saaimulation/Project-Aero/practice-lap-CAD/screenshots/3rdflap.png

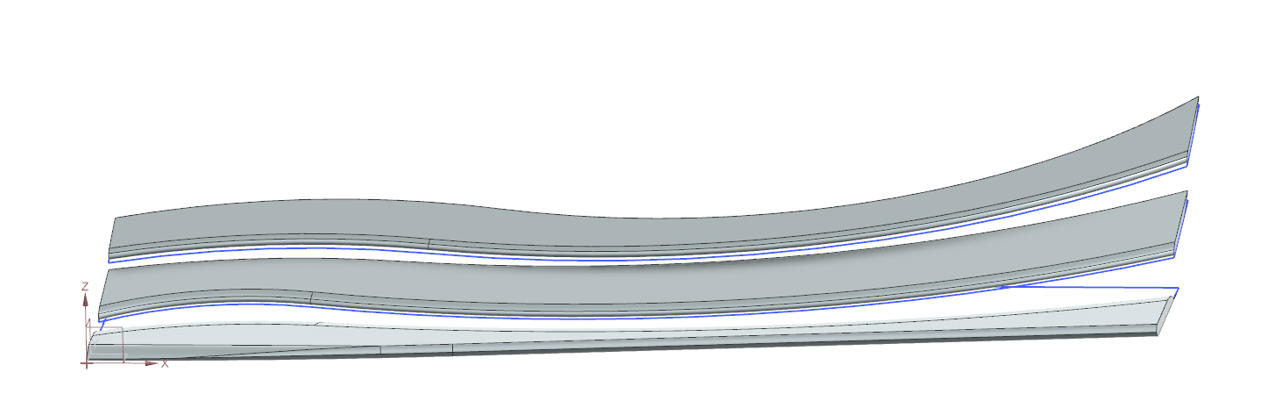
practice-lap-CAD/screenshots/3rdflap.png
