saaimulation/Project-Aero/practice-lap-CAD/screenshots/aerofoilshape.png

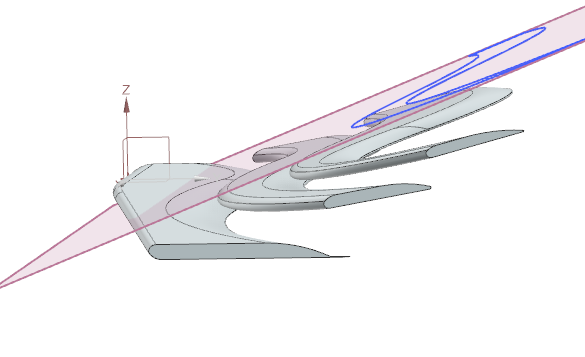
practice-lap-CAD/screenshots/aerofoilshape.png
