saaimulation/Project-Aero/practice-lap-CAD/screenshots/endplateedge.png

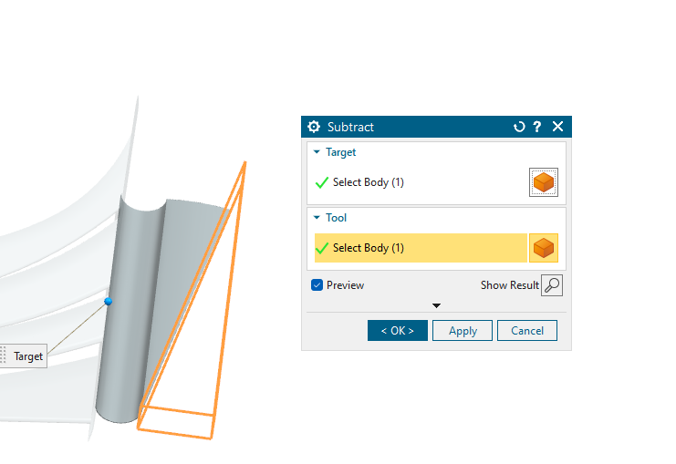
practice-lap-CAD/screenshots/endplateedge.png
