saaimulation/Project-Aero/practice-lap-CAD/screenshots/lines.png

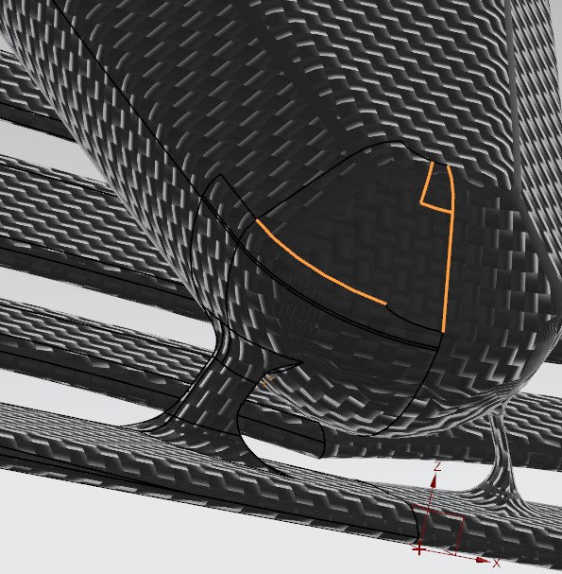
practice-lap-CAD/screenshots/lines.png
