saaimulation/Project-Aero/practice-lap-CAD/screenshots/sideview.png

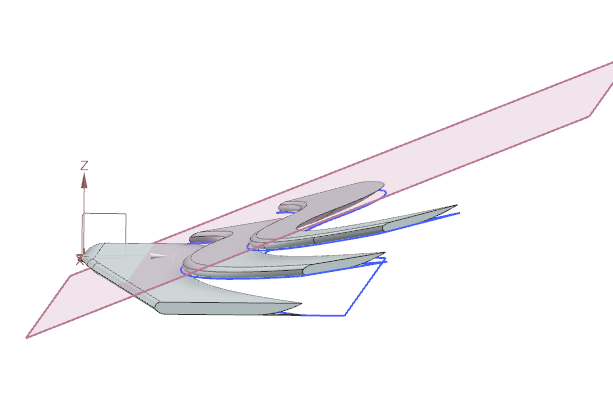
practice-lap-CAD/screenshots/sideview.png
