saaimulation/Project-Aero/qualifying-1-CFD/media/cfderror4.png

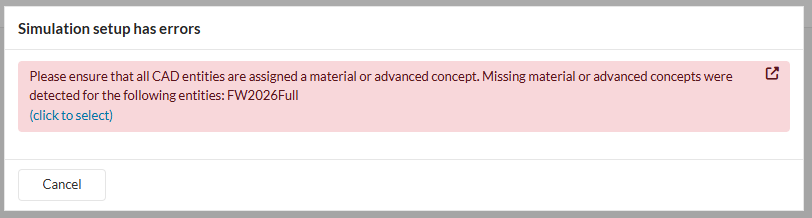
qualifying-1-CFD/media/cfderror4.png
