saaimulation/Project-Aero/sprint-3D-printing/images/finalprint.png

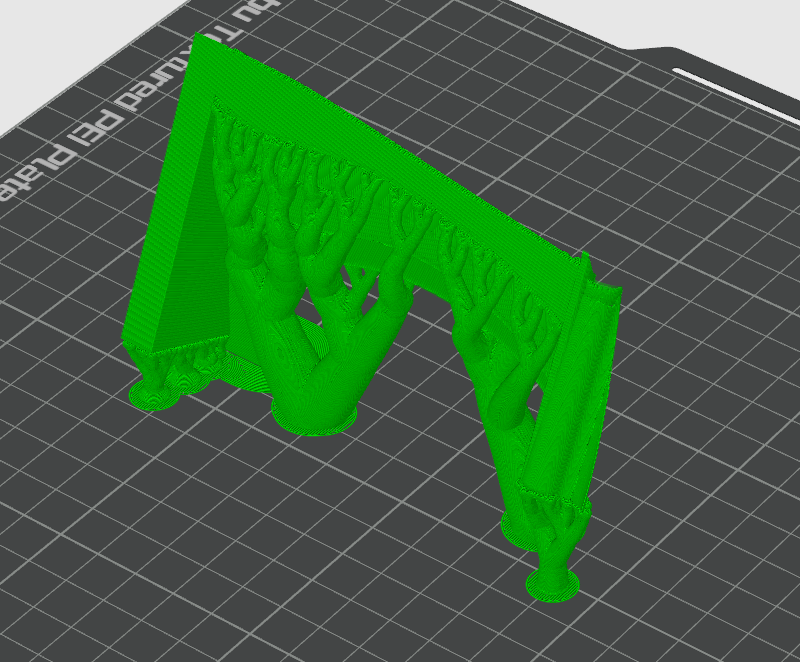
sprint-3D-printing/images/finalprint.png
