saaimulation/Project-Aero/sprint-3D-printing/images/key1.png

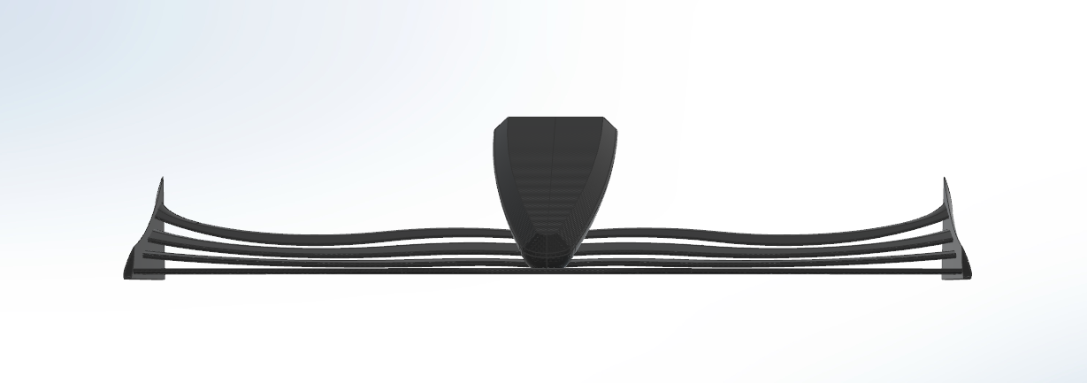
sprint-3D-printing/images/key1.png
